schnoog/Totally-over-engineered-filament-spool-balance/src/humidity.h

#pragma once


#include <esp32-hal.h>
#include <esp32-hal-ledc.h>

int pwmValue = 0;
const int freq = 23000;
const int ledChannel = 0;
const int resolution = 8;

float Humidity = 25.2;
float Temperature = 21.2;

int PumpPin1 = 47;
int PumpPin2 = 48;
int PumpState = 0;

float MinHum = 59.1;
float MaxHum = 61.0;

int AutoContol = 1;

#include <BME280I2C.h>
#include <Wire.h>

#define EEPROM_ADDR_MINHUM 12*sizeof(float)
#define EEPROM_ADDR_MAXHUM 13*sizeof(float)


void load_HumSettings(){
    float mtmp = 0;
    EEPROM.get(EEPROM_ADDR_MINHUM,mtmp);
    if(mtmp > 0.0){
        MinHum = mtmp;
    }
    EEPROM.get(EEPROM_ADDR_MAXHUM,mtmp);
    if(mtmp > 0.0){
        MaxHum = mtmp;
    }

}

void save_HumSettings(){
    EEPROM.put(EEPROM_ADDR_MINHUM, MinHum);
    EEPROM.commit();
    EEPROM.put(EEPROM_ADDR_MAXHUM, MaxHum);
    EEPROM.commit();
}

void set_MinHum(float NewMinHum){
    MinHum = NewMinHum;
    save_HumSettings();
}

void set_MaxHum(float NewMaxHum){
    MaxHum = NewMaxHum;
    save_HumSettings();
}


BME280I2C bme;    // Default : forced mode, standby time = 1000 ms
                  // Oversampling = pressure ×1, temperature ×1, humidity ×1, filter off,


int CurrPWM = 0;

void pumps_on(){
  if(PumpState == 0){
//    digitalWrite(PumpPin1,HIGH);  
    ledcWrite(ledChannel, 200);
//    digitalWrite(PumpPin2,HIGH);
    PumpState = 1;
    }
}

void pumps_off(){
  if(PumpState == 1){
//    digitalWrite(PumpPin1,LOW);
    ledcWrite(ledChannel, 0);
//    digitalWrite(PumpPin2,LOW);
    PumpState = 0;
    }
}


void bme_setup()
{
//    pinMode(PumpPin1,OUTPUT);
//    pinMode(PumpPin2,OUTPUT);
    ledcSetup(ledChannel, freq, resolution);
    ledcAttachPin(PumpPin1, ledChannel);



  Wire.begin();


  while(!bme.begin())
  {
    Serial.println("Could not find BME280 sensor!");
    delay(1000);
  }

  switch(bme.chipModel())
  {
     case BME280::ChipModel_BME280:
       Serial.println("Found BME280 sensor! Success.");
       break;
     case BME280::ChipModel_BMP280:
       Serial.println("Found BMP280 sensor! No Humidity available.");
       break;
     default:
       Serial.println("Found UNKNOWN sensor! Error!");
  }
  load_HumSettings();
}

void printBME280Data
(
   Stream* client
)
{
   float temp(NAN), hum(NAN), pres(NAN);

   BME280::TempUnit tempUnit(BME280::TempUnit_Celsius);
   BME280::PresUnit presUnit(BME280::PresUnit_Pa);

   bme.read(pres, temp, hum, tempUnit, presUnit);

   client->print("Temp: ");
   client->print(temp);
   Temperature = temp;
   client->print("°"+ String(tempUnit == BME280::TempUnit_Celsius ? 'C' :'F'));
   client->print("\t\tHumidity: ");
   client->print(hum);
   Humidity = hum;
   client->print("% RH");
   client->print("\t\tPressure: ");
   client->print(pres);
   client->println("Pa");

   //delay(1000);
}

unsigned long previousTimeHighHumidity = 0; // Variable to store the previous time humidity was above threshold
unsigned long previousTimeLowHumidity = 0;  // Variable to store the previous time humidity was below threshold
float aboveThresholdHumidity = 0;           // Variable to store the humidity when it crossed the threshold
float belowThresholdHumidity = 0;           // Variable to store the humidity when it crossed below the threshold

void bme_loop() {
    printBME280Data(&Serial);
    //delay(500);
    
    if (AutoContol == 1) {
        // Check if humidity is above the maximum threshold
        if (Humidity > MaxHum) {
            if (aboveThresholdHumidity == 0) { // If humidity just crossed the threshold
                aboveThresholdHumidity = Humidity;
                previousTimeHighHumidity = millis(); // Start the timer
            } else {
                // If humidity has been above the threshold for more than 60 seconds
                if (millis() - previousTimeHighHumidity >= 60000) {
                    pumps_on();
                }
            }
        } else {
            aboveThresholdHumidity = 0; // Reset the aboveThresholdHumidity if humidity falls below the threshold
        }
        
        // Check if humidity is below the minimum threshold
        if (Humidity < MinHum) {
            if (belowThresholdHumidity == 0) { // If humidity just crossed below the threshold
                belowThresholdHumidity = Humidity;
                previousTimeLowHumidity = millis(); // Start the timer
            } else {
                // If humidity has been below the threshold for more than 30 seconds
                if (millis() - previousTimeLowHumidity >= 30000) {
                    pumps_off();
                }
            }
        } else {
            belowThresholdHumidity = 0; // Reset the belowThresholdHumidity if humidity rises above the threshold
        }
    }
}



void bme_loopX()
{
   printBME280Data(&Serial);
   //delay(500);
   if(AutoContol == 1){
    if(Humidity > MaxHum) pumps_on();
    if(Humidity < MinHum) pumps_off();
   }
}
