schnoog/Totally-over-engineered-filament-spool-balance/src/displayinit.h

#pragma once

#define USE_HSPI_FOR_EPD
#define ENABLE_GxEPD2_GFX 0
#include <GxEPD2_BW.h>
#include <Fonts/FreeMonoBold9pt7b.h>
#include <Fonts/FreeMonoBold12pt7b.h>
#include <Fonts/FreeMonoBold18pt7b.h>

#include <Fonts/FreeMonoBold24pt7b.h>
#include <Fonts/FreeMono9pt7b.h>
// select the display class (only one), matching the kind of display panel
#define GxEPD2_DISPLAY_CLASS GxEPD2_BW
#define GxEPD2_DRIVER_CLASS GxEPD2_420     // GDEW042T2   400x300, UC8176 (IL0398), (WFT042CZ15)
//#define GxEPD2_DRIVER_CLASS GxEPD2_420_M01 // GDEW042M01  400x300, UC8176 (IL0398), (WFT042CZ15)
//#define GxEPD2_DRIVER_CLASS GxEPD2_420_GDEY042T81 // GDEY042T81 400x300, SSD1683 (no inking)
//#define GxEPD2_DRIVER_CLASS GxEPD2_420c     // GDEW042Z15  400x300, UC8176 (IL0398), (WFT0420CZ15)
//#define GxEPD2_DRIVER_CLASS GxEPD2_420c_Z21 // GDEQ042Z21  400x300, UC8276, (hidden)
//#define GxEPD2_DRIVER_CLASS GxEPD2_420c_GDEY0420F51 // GDEY0420F51 400x300, HX8717 (no inking)
#define GxEPD2_BW_IS_GxEPD2_BW true
#define IS_GxEPD(c, x) (c##x)
#define IS_GxEPD2_BW(x) IS_GxEPD(GxEPD2_BW_IS_, x)
#define MAX_DISPLAY_BUFFER_SIZE 65536ul // e.g.
#define MAX_HEIGHT(EPD) (EPD::HEIGHT <= MAX_DISPLAY_BUFFER_SIZE / (EPD::WIDTH / 8) ? EPD::HEIGHT : MAX_DISPLAY_BUFFER_SIZE / (EPD::WIDTH / 8))
GxEPD2_DISPLAY_CLASS<GxEPD2_DRIVER_CLASS, MAX_HEIGHT(GxEPD2_DRIVER_CLASS)> display(GxEPD2_DRIVER_CLASS(/*CS=*/ 3, /*DC=*/ 9, /*RST=*/ 10, /*BUSY=*/ 11));
//GxEPD2_DISPLAY_CLASS<GxEPD2_DRIVER_CLASS, MAX_HEIGHT(GxEPD2_DRIVER_CLASS)> display(GxEPD2_DRIVER_CLASS(/*CS=*/ 15, /*DC=*/ 9, /*RST=*/ 10, /*BUSY=*/ 11));



#include "bitmaps/Bitmaps400x300.h" // 4.2"  b/w
#if defined(ESP32) && defined(USE_HSPI_FOR_EPD)

SPIClass hspi(HSPI);
#endif

#ifdef _GxBitmaps400x300_H_
void drawBitmaps400x300()
{
#if !defined(__AVR)
  const unsigned char* bitmaps[] =
  {
    Bitmap400x300_1, Bitmap400x300_2
  };
#else
  const unsigned char* bitmaps[] = {}; // not enough code space
#endif
  if (display.epd2.panel == GxEPD2::GDEW042T2)
  {
    for (uint16_t i = 0; i < sizeof(bitmaps) / sizeof(char*); i++)
    {
      display.firstPage();
      do
      {
        display.fillScreen(GxEPD_WHITE);
        display.drawInvertedBitmap(0, 0, bitmaps[i], display.epd2.WIDTH, display.epd2.HEIGHT, GxEPD_BLACK);
      }
      while (display.nextPage());
      delay(2000);
    }
  }
}
#endif


struct bitmap_pair
{
  const unsigned char* black;
  const unsigned char* red;
};



void ePaper_setup(){
  Serial.println("setup ePaper");
  hspi.begin(13, 12, 14, 15); // remap hspi for EPD (swap pins)
  display.epd2.selectSPI(hspi, SPISettings(4000000, MSBFIRST, SPI_MODE0));
  display.init(115200);
  delay(1000);
}
